gurunishaanth/Joint-Locking-Mechanism-for-Soft-Robotic-Finger/Full Finger/Finger mold v8.2 1 pt1 single mold.SLDPRT

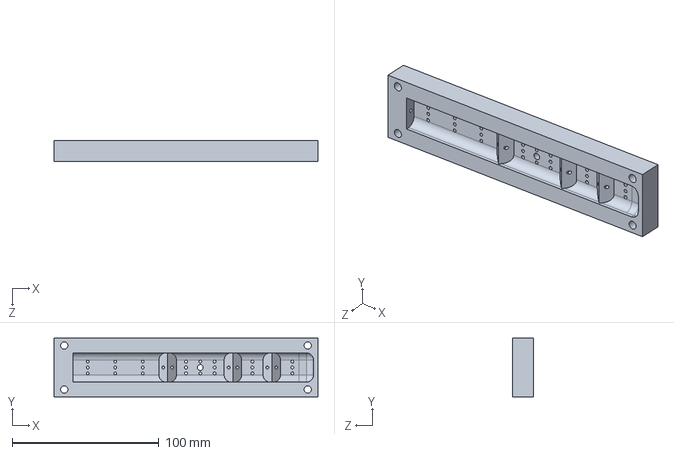
[picture p59: CAD file, 2026-09-08]
Full Finger/Finger mold v8.2 1 pt1 single mold.SLDPRT
180.0 x 40.0 x 14.0 mm
