gurunishaanth/Joint-Locking-Mechanism-for-Soft-Robotic-Finger/LA/shaft LA V78.SLDPRT

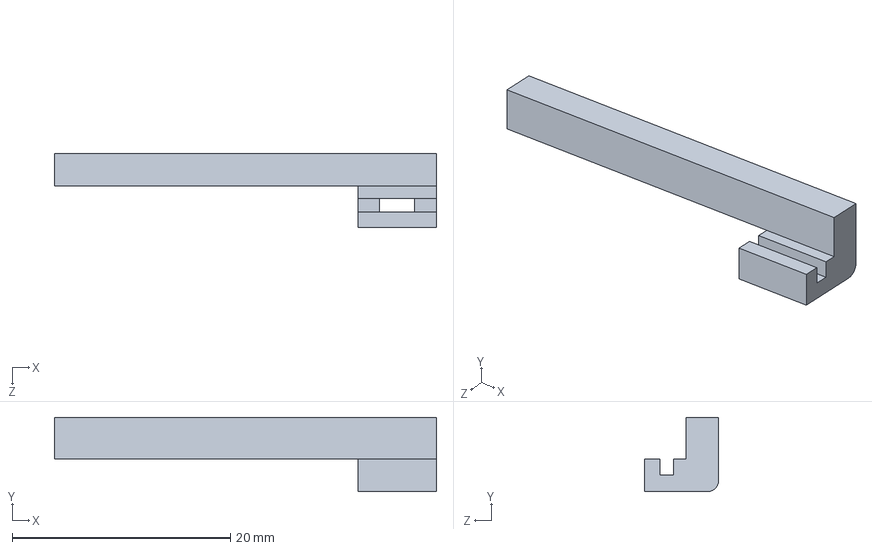
[picture p60: CAD file, 2026-09-08]
LA/shaft LA V78.SLDPRT
35.0 x 6.80 x 6.80 mm
