gurunishaanth/Joint-Locking-Mechanism-for-Soft-Robotic-Finger/RP/Lid 2 V2.SLDPRT

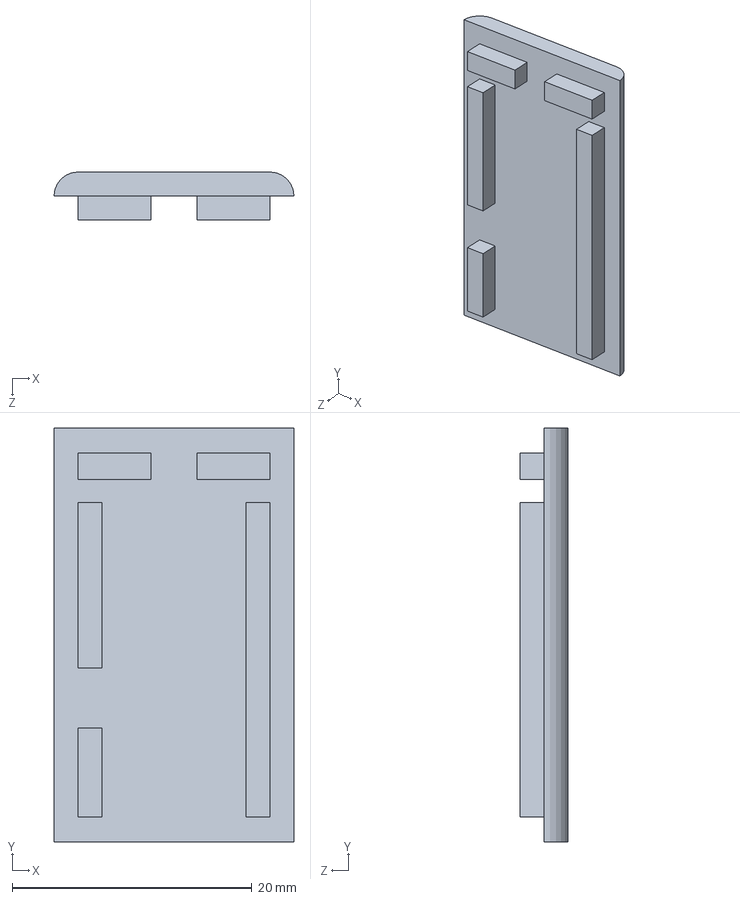
[picture p61: CAD file, 2026-09-08]
RP/Lid 2 V2.SLDPRT
20.0 x 34.5 x 4.00 mm
