gurunishaanth/Joint-Locking-Mechanism-for-Soft-Robotic-Finger/RP/STL/Rack V11 RP.STL

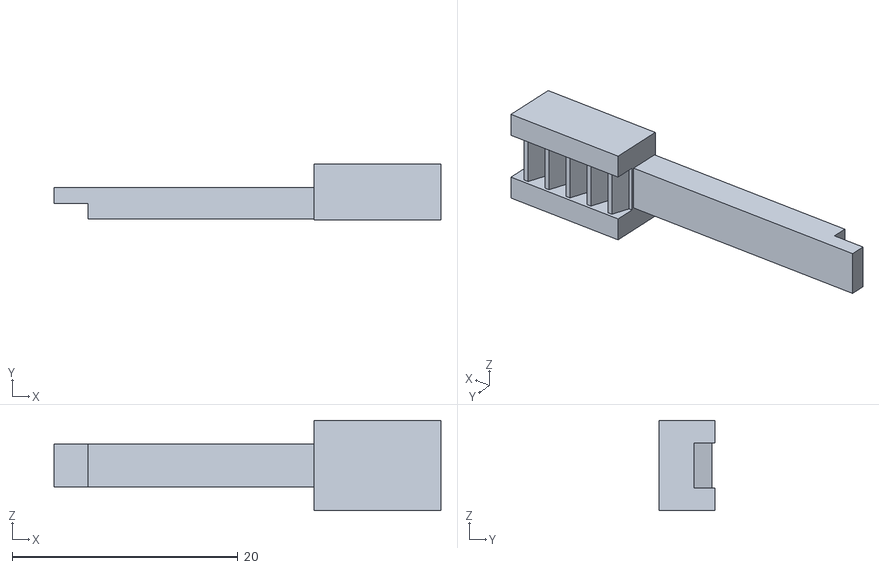
[picture p62: CAD file, 2026-09-08]
RP/STL/Rack V11 RP.STL
34.2 x 5.00 x 8.00
