gurunishaanth/Joint-Locking-Mechanism-for-Soft-Robotic-Finger/EM/Base 2 EM P2 V5.SLDPRT

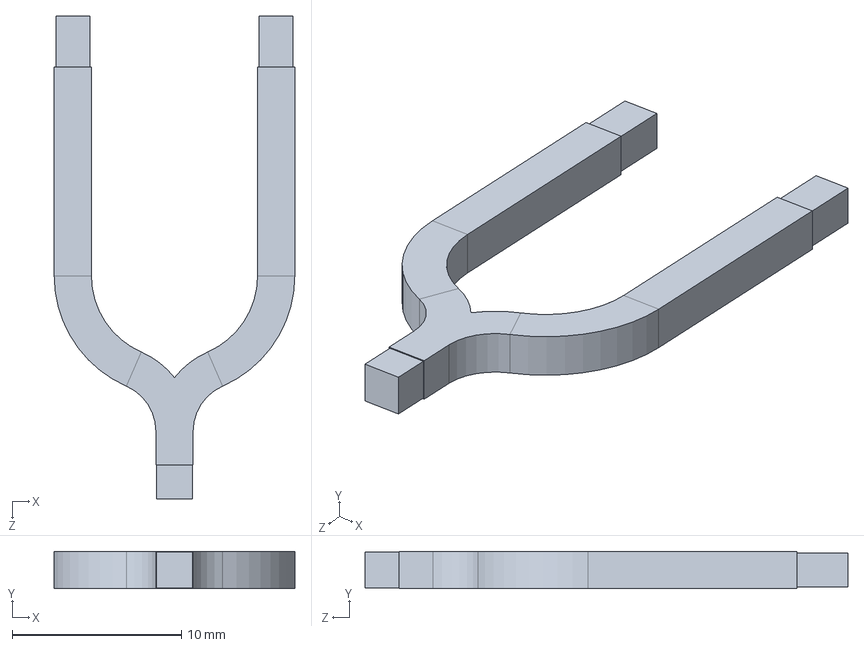
[picture p63: CAD file, 2026-09-08]
EM/Base 2 EM P2 V5.SLDPRT
14.2 x 2.20 x 28.5 mm
