gurunishaanth/Joint-Locking-Mechanism-for-Soft-Robotic-Finger/EM/STL/Base 4 EM V4.STL

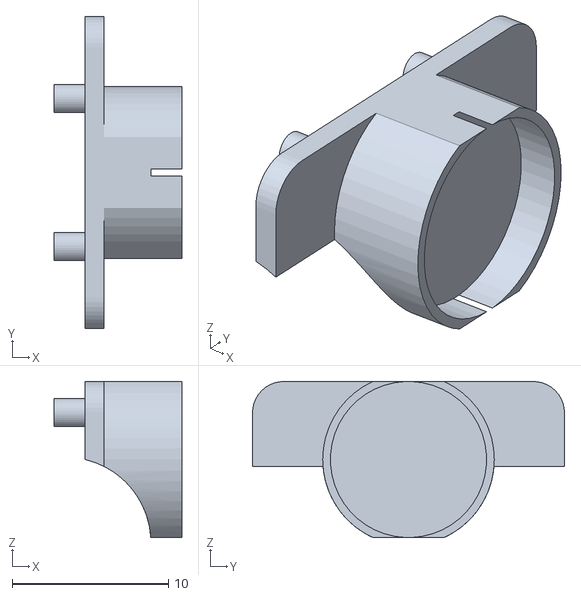
[picture p64: CAD file, 2026-09-08]
EM/STL/Base 4 EM V4.STL
8.20 x 20.0 x 10.0
