gurunishaanth/Joint-Locking-Mechanism-for-Soft-Robotic-Finger/finger base/finger base flex v7 p2.SLDPRT

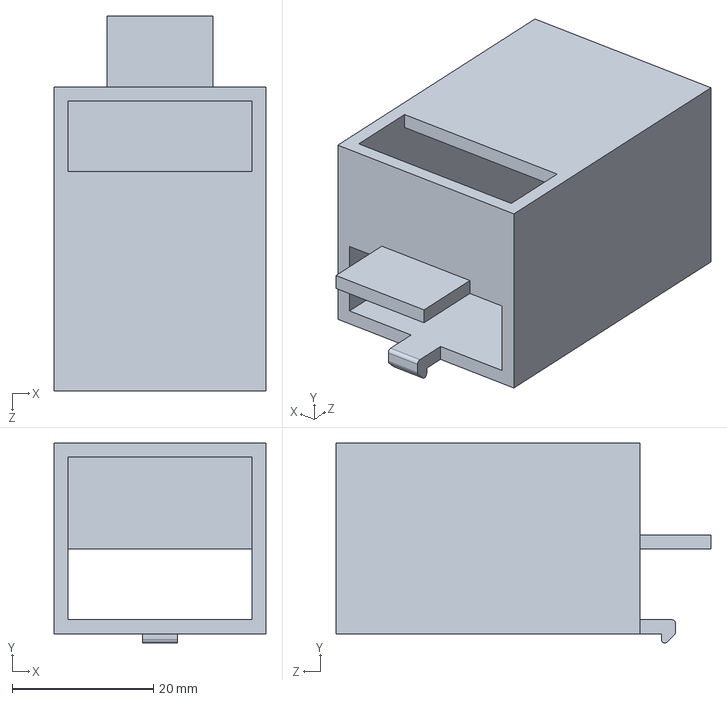
[picture p65: CAD file, 2026-09-08]
finger base/finger base flex v7 p2.SLDPRT
30.0 x 28.3 x 53.0 mm
