gurunishaanth/Joint-Locking-Mechanism-for-Soft-Robotic-Finger/Full Finger EM/Base 2 EM V4 P1.SLDPRT

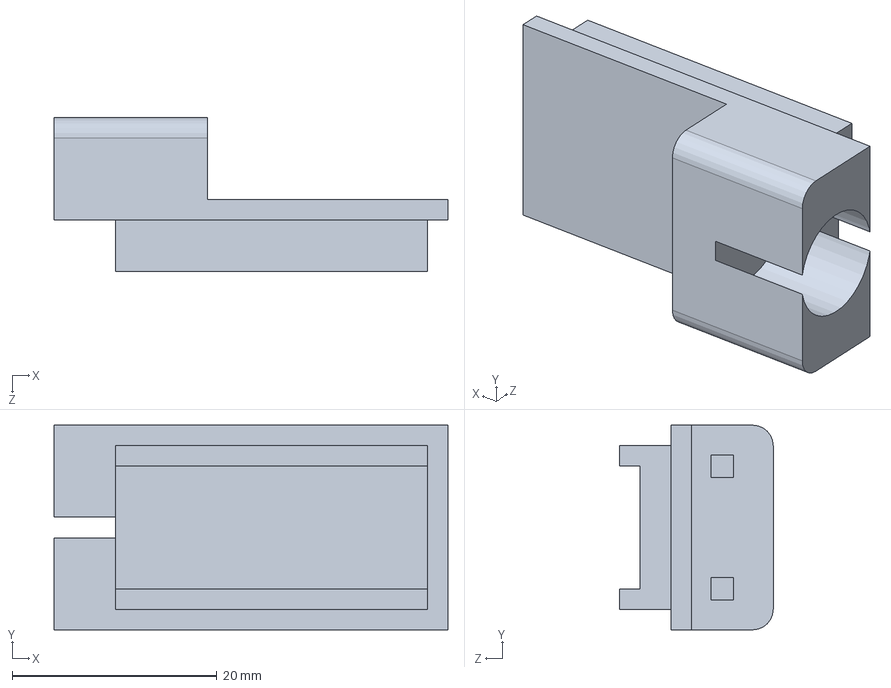
[picture p66: CAD file, 2026-09-08]
Full Finger EM/Base 2 EM V4 P1.SLDPRT
38.5 x 20.0 x 15.0 mm
