gurunishaanth/Joint-Locking-Mechanism-for-Soft-Robotic-Finger/Full Finger EM/stl/Base 3 EM V4 P1.STL

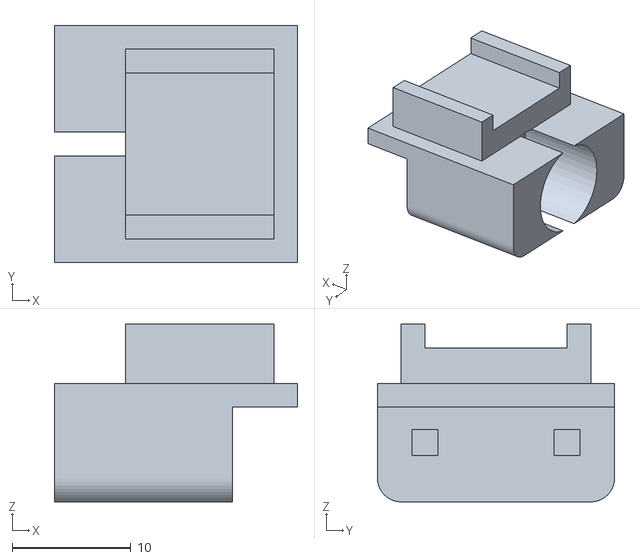
[picture p67: CAD file, 2026-09-08]
Full Finger EM/stl/Base 3 EM V4 P1.STL
20.5 x 20.0 x 15.0
