gurunishaanth/Joint-Locking-Mechanism-for-Soft-Robotic-Finger/Full finger LA/stl/cork v2.STL

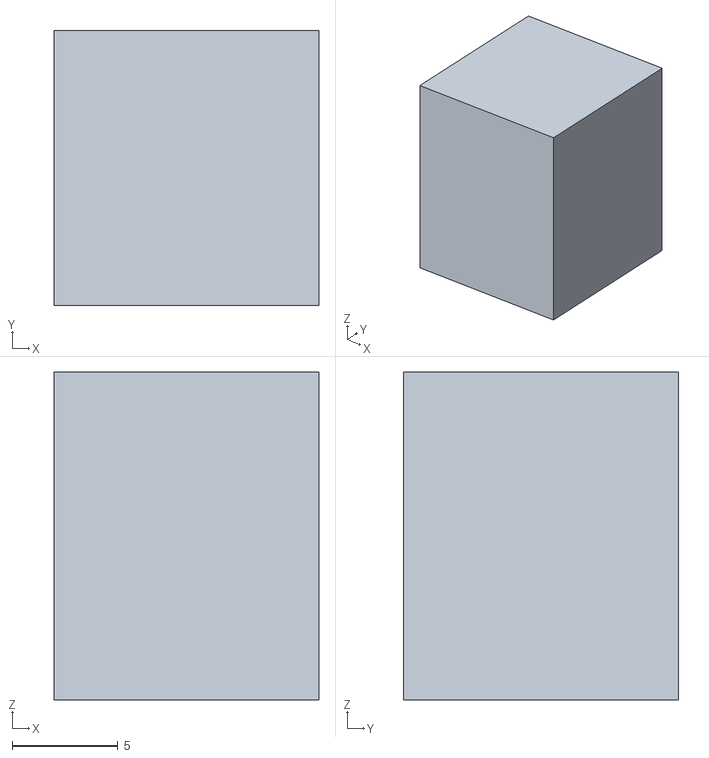
[picture p68: CAD file, 2026-09-08]
Full finger LA/stl/cork v2.STL
12.5 x 13.0 x 15.5
