gurunishaanth/Joint-Locking-Mechanism-for-Soft-Robotic-Finger/Full Finger/Finger mold v8 1 pt2 single mold s2.SLDPRT

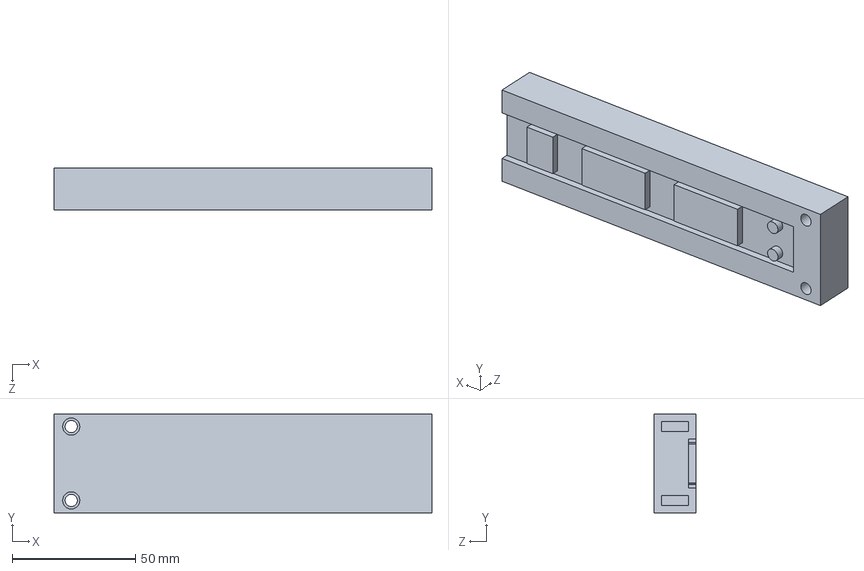
[picture p69: CAD file, 2026-09-08]
Full Finger/Finger mold v8 1 pt2 single mold s2.SLDPRT
153.5 x 40.0 x 17.0 mm
