gurunishaanth/Joint-Locking-Mechanism-for-Soft-Robotic-Finger/LA/Lid LA V8.SLDPRT

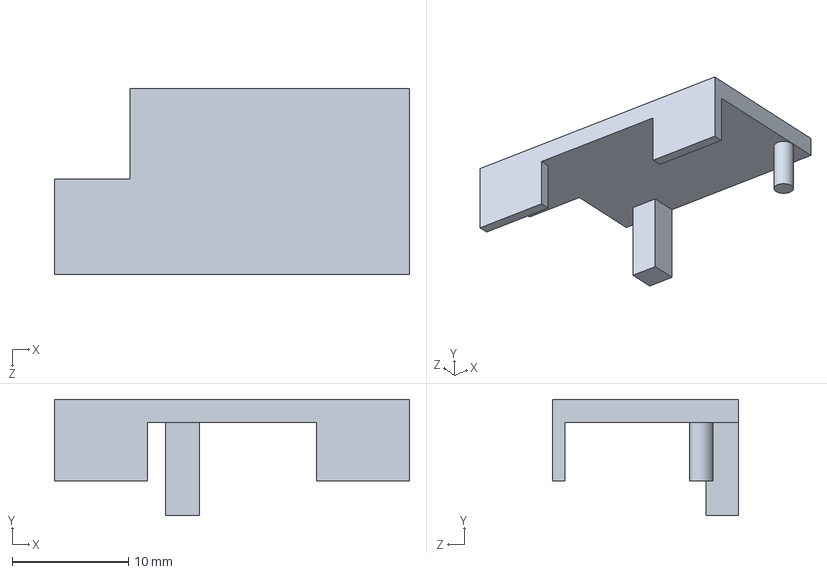
[picture p70: CAD file, 2026-09-08]
LA/Lid LA V8.SLDPRT
30.5 x 10.0 x 16.0 mm
