gurunishaanth/Joint-Locking-Mechanism-for-Soft-Robotic-Finger/RP/Lock V3 RP.SLDPRT

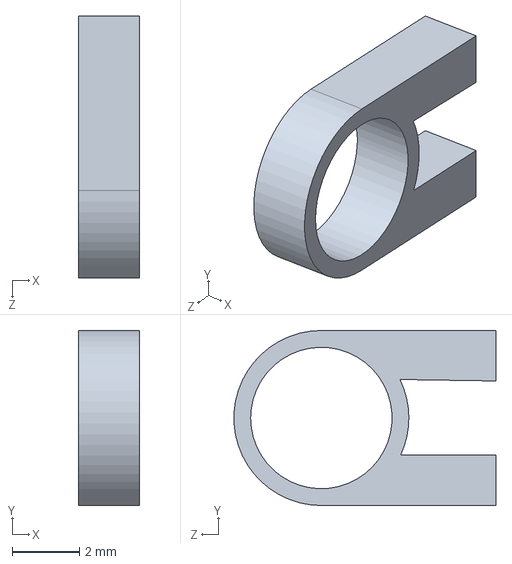
[picture p71: CAD file, 2026-09-08]
RP/Lock V3 RP.SLDPRT
1.80 x 5.20 x 7.78 mm
