gurunishaanth/Joint-Locking-Mechanism-for-Soft-Robotic-Finger/EM/Base 2 EM V3.SLDPRT

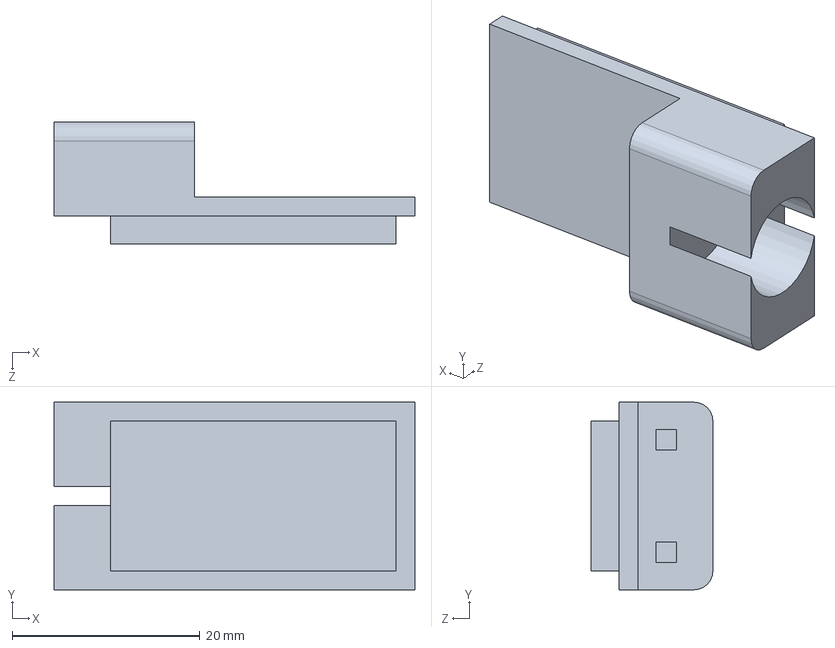
[picture p72: CAD file, 2026-09-08]
EM/Base 2 EM V3.SLDPRT
38.5 x 20.0 x 13.0 mm
