gurunishaanth/Joint-Locking-Mechanism-for-Soft-Robotic-Finger/finger base/finger base flex lid v4.SLDPRT

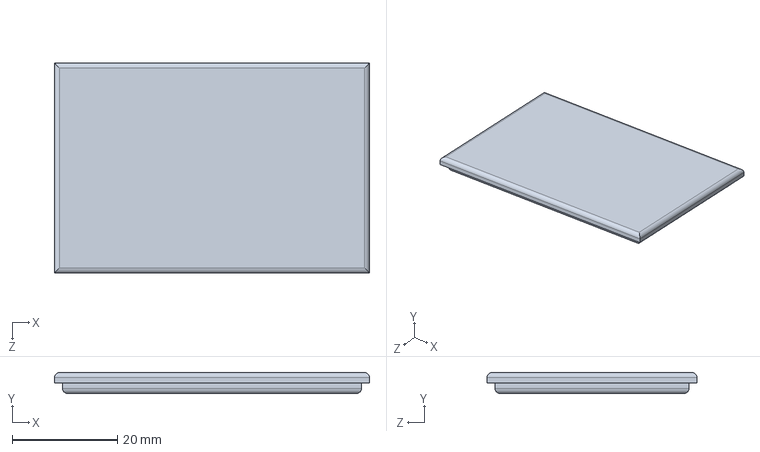
[picture p73: CAD file, 2026-09-08]
finger base/finger base flex lid v4.SLDPRT
60.0 x 4.00 x 40.0 mm
