gurunishaanth/Joint-Locking-Mechanism-for-Soft-Robotic-Finger/Full finger LA/Lid LA V9 p2.SLDPRT

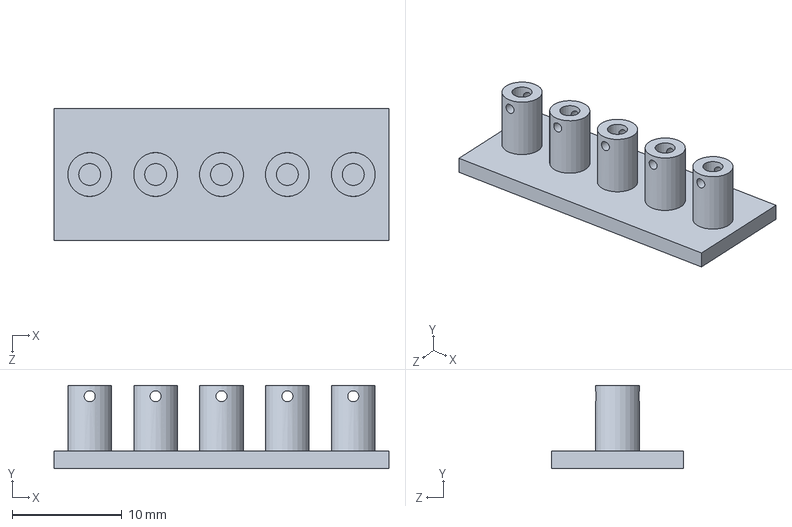
[picture p74: CAD file, 2026-09-08]
Full finger LA/Lid LA V9 p2.SLDPRT
30.5 x 7.60 x 12.0 mm
