gurunishaanth/Joint-Locking-Mechanism-for-Soft-Robotic-Finger/Full finger LA/stl/Lid LA V10 p2.STL

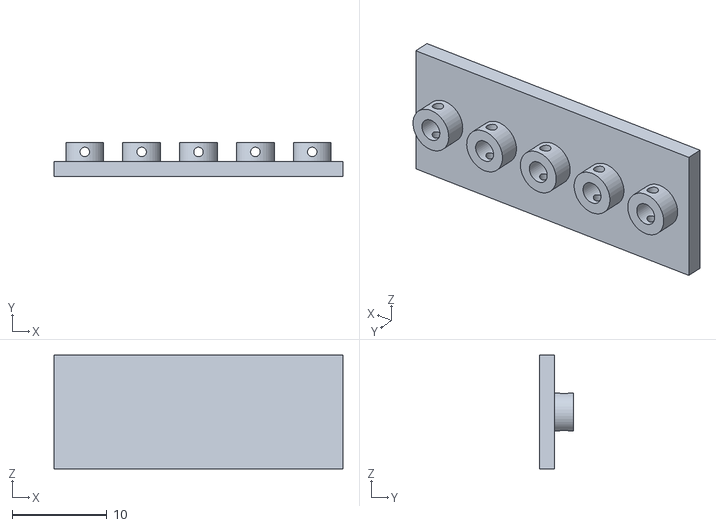
[picture p75: CAD file, 2026-09-08]
Full finger LA/stl/Lid LA V10 p2.STL
30.5 x 3.60 x 12.0
