gurunishaanth/Joint-Locking-Mechanism-for-Soft-Robotic-Finger/Full Finger/Finger mold v8 1 pt2 single mold s1.SLDPRT

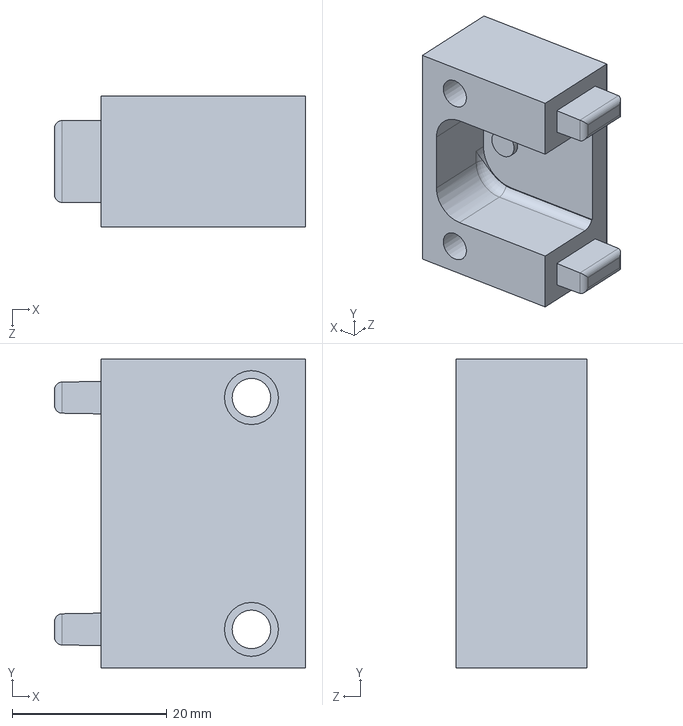
[picture p76: CAD file, 2026-09-08]
Full Finger/Finger mold v8 1 pt2 single mold s1.SLDPRT
32.5 x 40.0 x 17.0 mm
