gurunishaanth/Joint-Locking-Mechanism-for-Soft-Robotic-Finger/RP/base V8 RP.SLDPRT

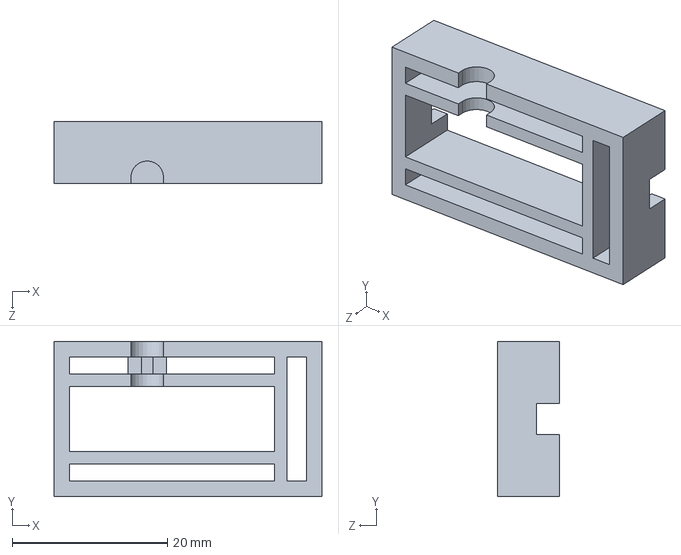
[picture p77: CAD file, 2026-09-08]
RP/base V8 RP.SLDPRT
34.5 x 20.0 x 8.00 mm
