gurunishaanth/Joint-Locking-Mechanism-for-Soft-Robotic-Finger/finger base/servo fixture.SLDPRT

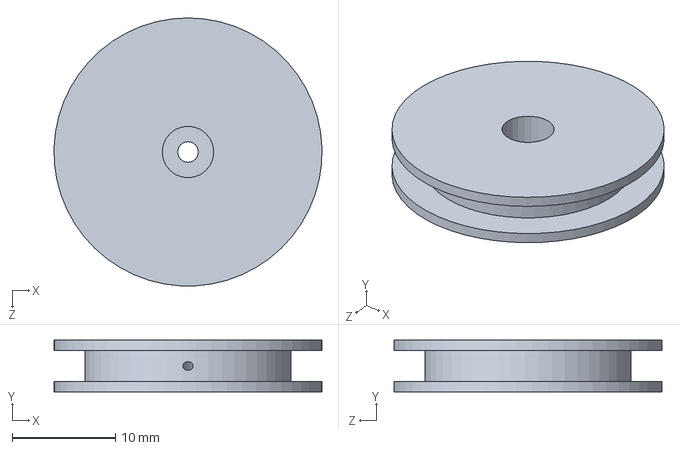
[picture p78: CAD file, 2026-09-08]
finger base/servo fixture.SLDPRT
26.0 x 5.00 x 26.0 mm
