gurunishaanth/Joint-Locking-Mechanism-for-Soft-Robotic-Finger/Full finger LA/Finger mold LA v8 1 pt1 single mold s2 v4.SLDPRT

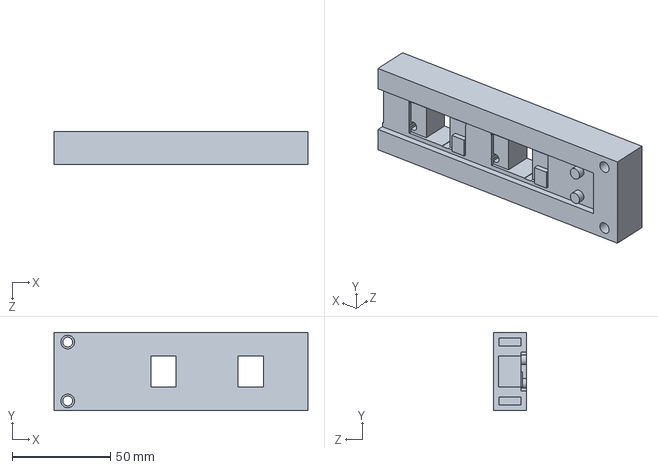
[picture p79: CAD file, 2026-09-08]
Full finger LA/Finger mold LA v8 1 pt1 single mold s2 v4.SLDPRT
129.5 x 40.0 x 17.0 mm
