gurunishaanth/Joint-Locking-Mechanism-for-Soft-Robotic-Finger/LA/Base LA V10.SLDPRT

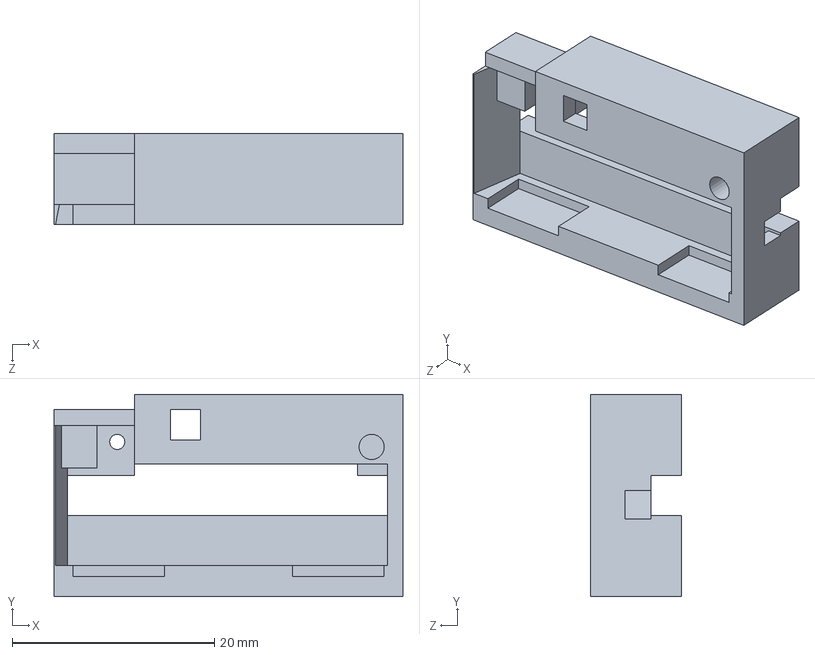
[picture p80: CAD file, 2026-09-08]
LA/Base LA V10.SLDPRT
34.5 x 20.0 x 9.00 mm
