gurunishaanth/Joint-Locking-Mechanism-for-Soft-Robotic-Finger/RP/gear RP v4.SLDPRT

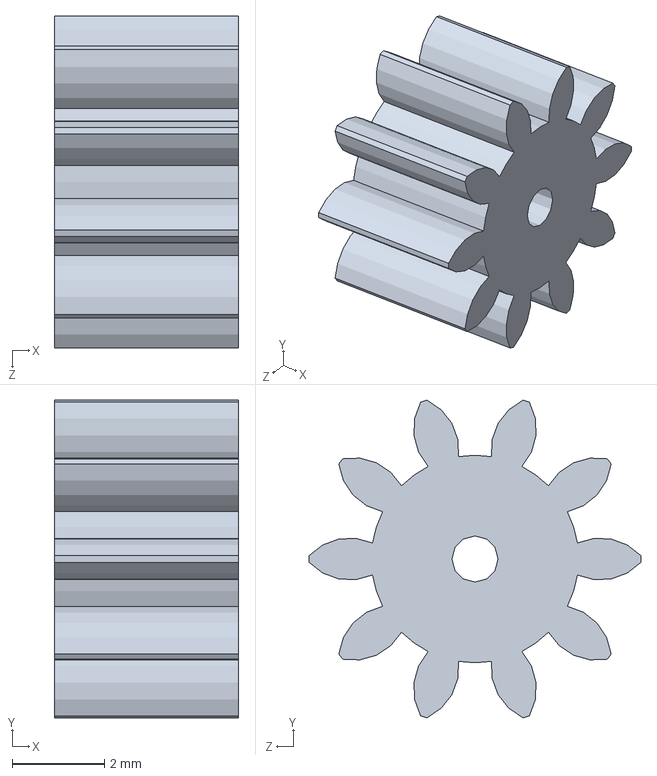
[picture p81: CAD file, 2026-09-08]
RP/gear RP v4.SLDPRT
4.00 x 6.89 x 7.20 mm
