gurunishaanth/Joint-Locking-Mechanism-for-Soft-Robotic-Finger/Full finger LA/cork.SLDPRT

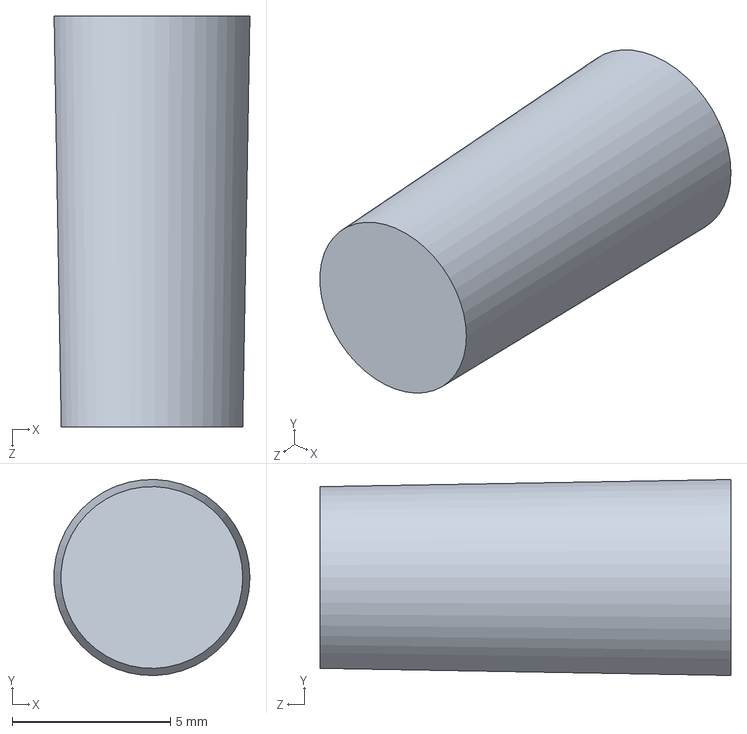
[picture p82: CAD file, 2026-09-08]
Full finger LA/cork.SLDPRT
6.20 x 6.20 x 13.0 mm
