gurunishaanth/Joint-Locking-Mechanism-for-Soft-Robotic-Finger/RP/Lid V6 RP.SLDPRT

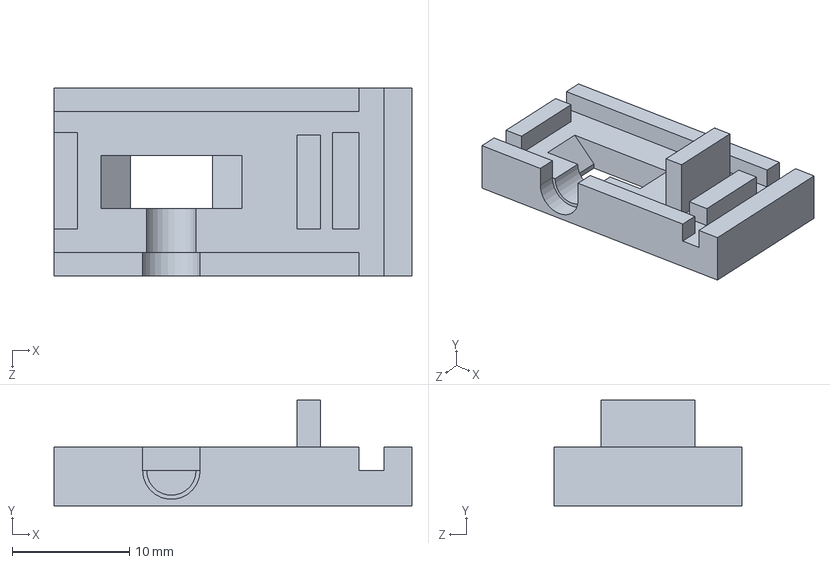
[picture p83: CAD file, 2026-09-08]
RP/Lid V6 RP.SLDPRT
30.5 x 9.00 x 16.0 mm
