gurunishaanth/Joint-Locking-Mechanism-for-Soft-Robotic-Finger/finger base/finger base flex v6.SLDPRT

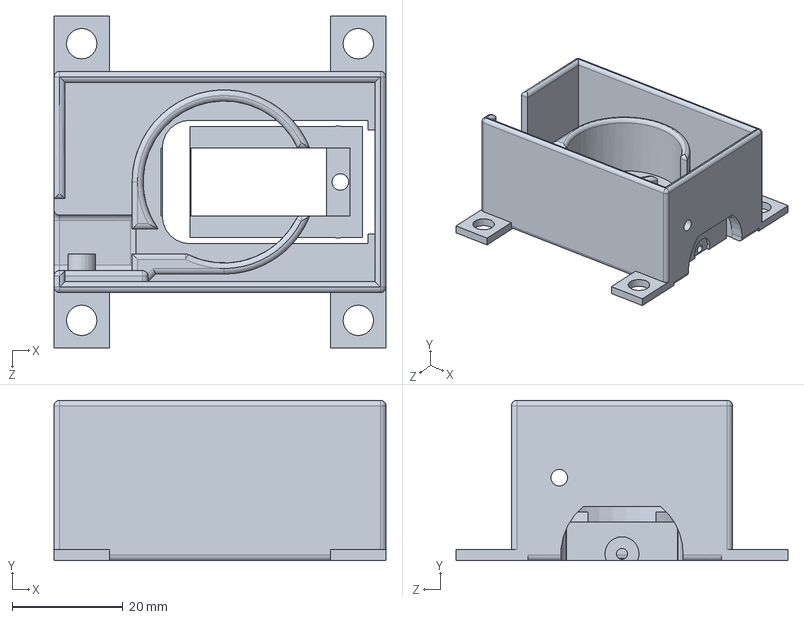
[picture p84: CAD file, 2026-09-08]
finger base/finger base flex v6.SLDPRT
60.0 x 29.0 x 60.0 mm
