gurunishaanth/Joint-Locking-Mechanism-for-Soft-Robotic-Finger/Full finger LA/Base 3 LA V4.SLDPRT

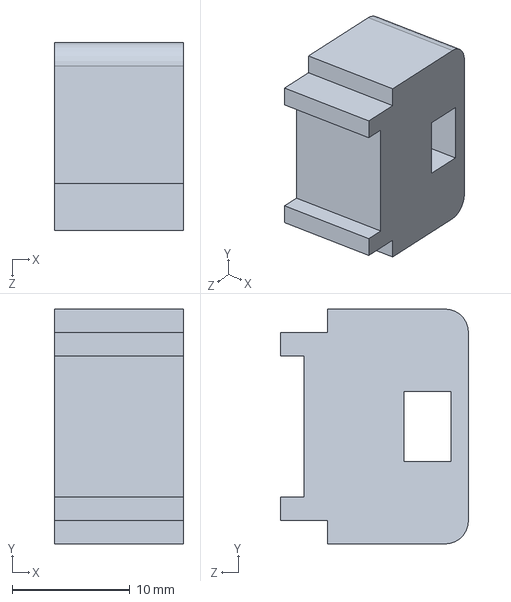
[picture p85: CAD file, 2026-09-08]
Full finger LA/Base 3 LA V4.SLDPRT
11.0 x 20.0 x 16.0 mm
