gurunishaanth/Joint-Locking-Mechanism-for-Soft-Robotic-Finger/Full finger LA/Finger mold LA v8 1 pt1 single mold s3 v2.SLDPRT

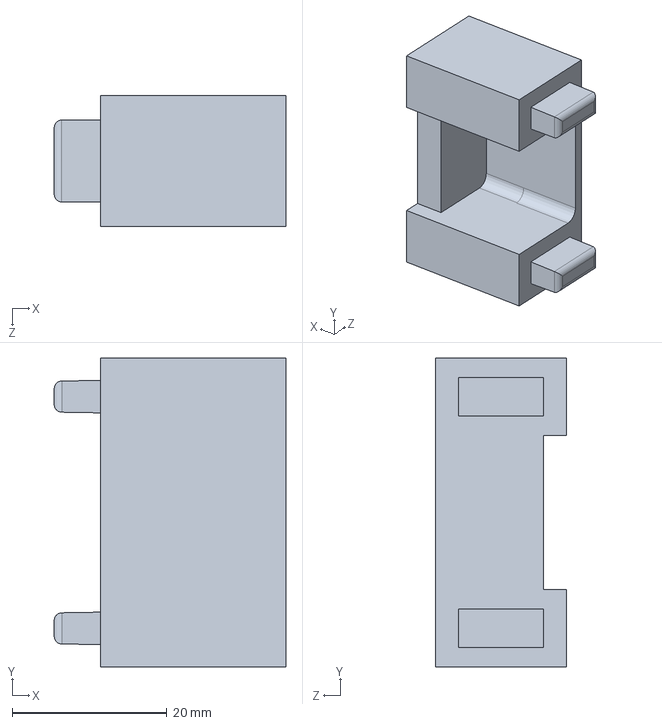
[picture p86: CAD file, 2026-09-08]
Full finger LA/Finger mold LA v8 1 pt1 single mold s3 v2.SLDPRT
30.0 x 40.0 x 17.0 mm
