gurunishaanth/Joint-Locking-Mechanism-for-Soft-Robotic-Finger/Full Finger EM/Base 2 EM P1 V5.SLDPRT

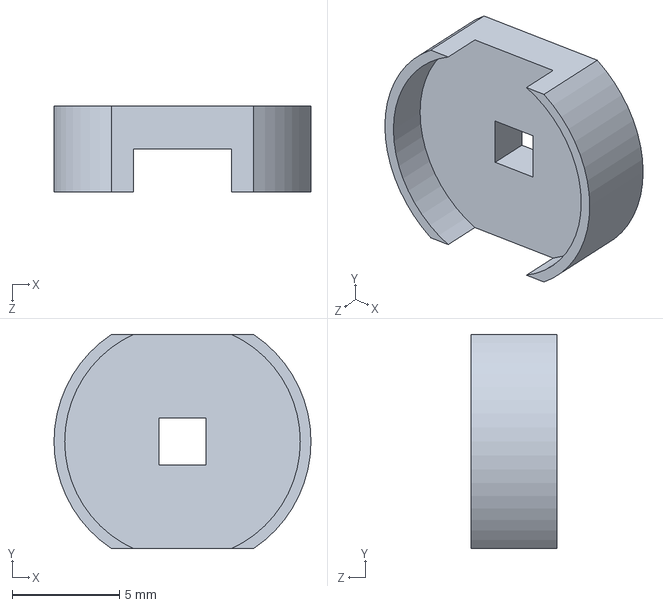
[picture p87: CAD file, 2026-09-08]
Full Finger EM/Base 2 EM P1 V5.SLDPRT
12.0 x 10.0 x 4.00 mm
