gurunishaanth/Joint-Locking-Mechanism-for-Soft-Robotic-Finger/Full finger LA/Base 3 LA V4 P2.SLDPRT

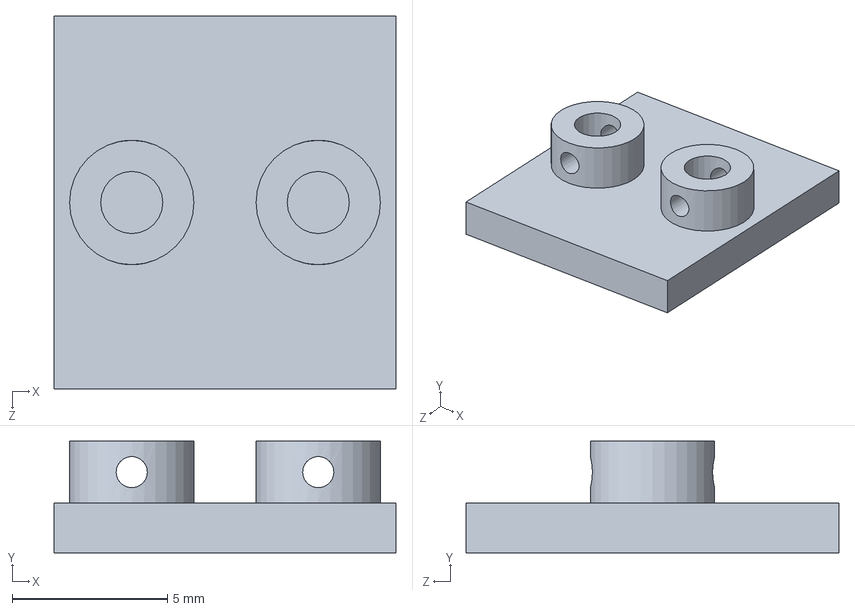
[picture p88: CAD file, 2026-09-08]
Full finger LA/Base 3 LA V4 P2.SLDPRT
11.0 x 3.60 x 12.0 mm
