gurunishaanth/Joint-Locking-Mechanism-for-Soft-Robotic-Finger/Full finger LA/Lid LA V9.SLDPRT

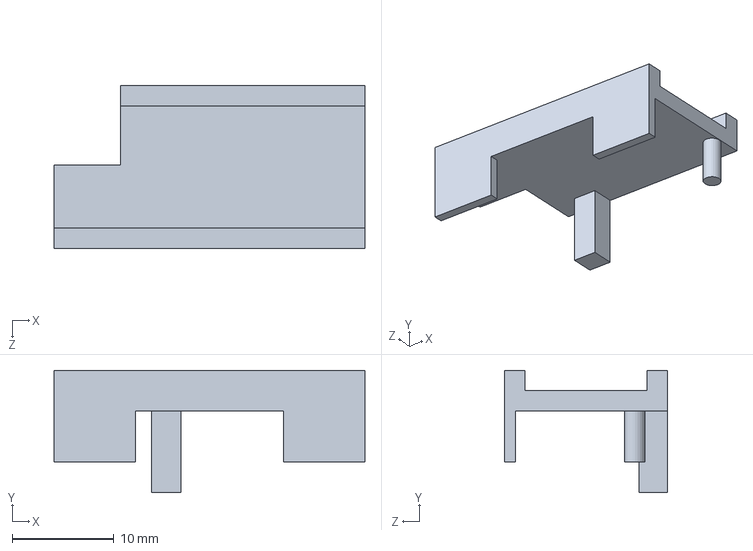
[picture p89: CAD file, 2026-09-08]
Full finger LA/Lid LA V9.SLDPRT
30.5 x 12.0 x 16.0 mm
