gurunishaanth/Joint-Locking-Mechanism-for-Soft-Robotic-Finger/Full finger LA/Lid LA.SLDPRT

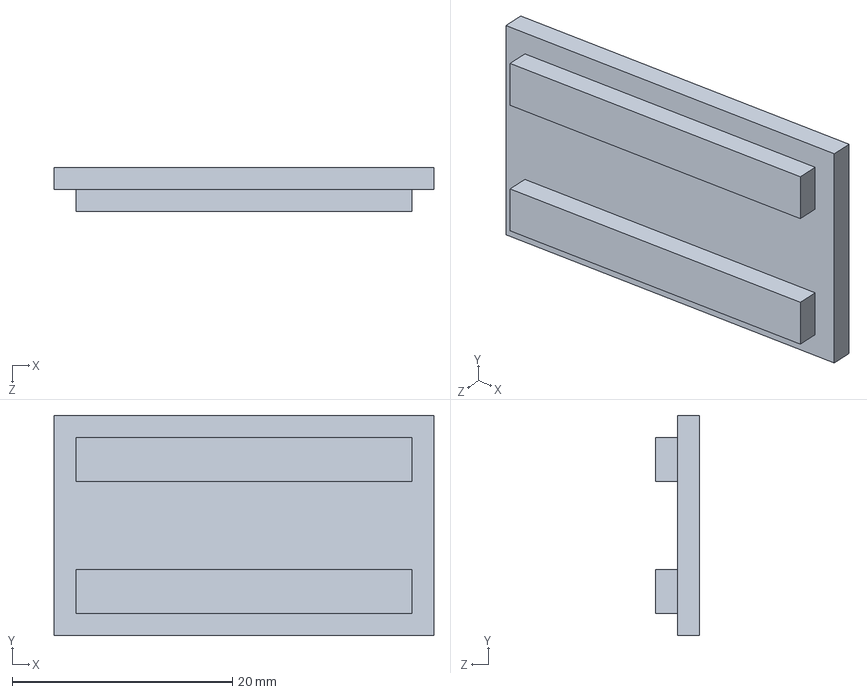
[picture p90: CAD file, 2026-09-08]
Full finger LA/Lid LA.SLDPRT
34.5 x 20.0 x 4.00 mm
