gurunishaanth/Joint-Locking-Mechanism-for-Soft-Robotic-Finger/finger base/new base.SLDASM

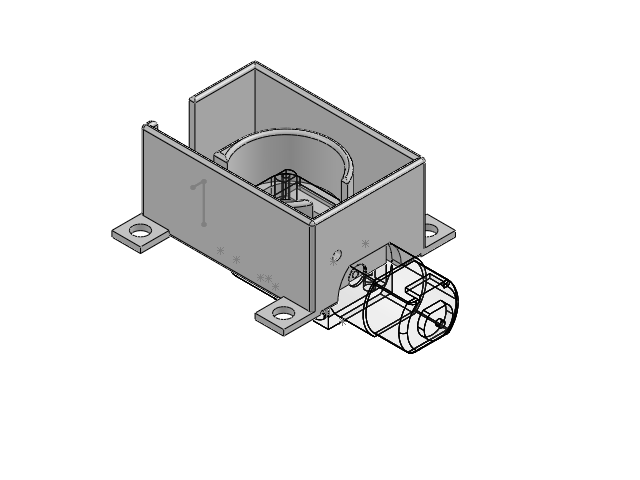
[picture p91: CAD file, 2026-09-08]
finger base/new base.SLDASM
finger base flex v6
motor.step
