gurunishaanth/Joint-Locking-Mechanism-for-Soft-Robotic-Finger/codes/LA_Arduino_test_1/LA_Arduino_test_1.ino

// Example sketch to control a stepper motor with A4988 stepper motor driver 
// and Arduino without a library. 
// www.makerguides.com

// Define stepper motor connections and steps per revolution:
#define dirPin 9
#define stepPin 8
#define stepsPerRevolution 500
#define n 10
void setup() {
  // Declare pins as output:
  pinMode(stepPin, OUTPUT);
  pinMode(dirPin, OUTPUT);
}

void loop() {
  // Set the spinning direction clockwise:
  digitalWrite(dirPin, LOW);

  // Spin the stepper motor 5 revolutions fast:
  for (int i = 0; i < n * stepsPerRevolution; i++) {
    // These four lines result in 1 step:
    digitalWrite(stepPin, HIGH);
    delayMicroseconds(500);
    digitalWrite(stepPin, LOW);
    delayMicroseconds(500);
  }

  delay(1000);

  // Set the spinning direction counterclockwise:
  digitalWrite(dirPin, HIGH );

  //Spin the stepper motor 5 revolutions fast:
  for (int i = 0; i < n * stepsPerRevolution; i++) {
    // These four lines result in 1 step:
    digitalWrite(stepPin, HIGH);
    delayMicroseconds(500);
    digitalWrite(stepPin, LOW);
    delayMicroseconds(500);
  }

  delay(1000);
}
