gurunishaanth/Joint-Locking-Mechanism-for-Soft-Robotic-Finger/codes/RP_Arduino_test_1/RP_Arduino_test_1.ino

int IN1 = 3;
int IN2 = 4;

void setup() {
  pinMode(IN1, OUTPUT);
  pinMode(IN2, OUTPUT);
}

void loop() {
  // Forward
  digitalWrite(IN1, HIGH);
  digitalWrite(IN2, LOW);
  delay(200);

  // Stop
  digitalWrite(IN1, LOW);
  digitalWrite(IN2, LOW);
  delay(1000);

  // Backward
  digitalWrite(IN1, LOW);
  digitalWrite(IN2, HIGH);
  delay(200);

  // Stop
  digitalWrite(IN1, LOW);
  digitalWrite(IN2, LOW);
  delay(200);
}
